lasr-lab/mistac/design/distalEnd/cartridgeInnerMesh.step

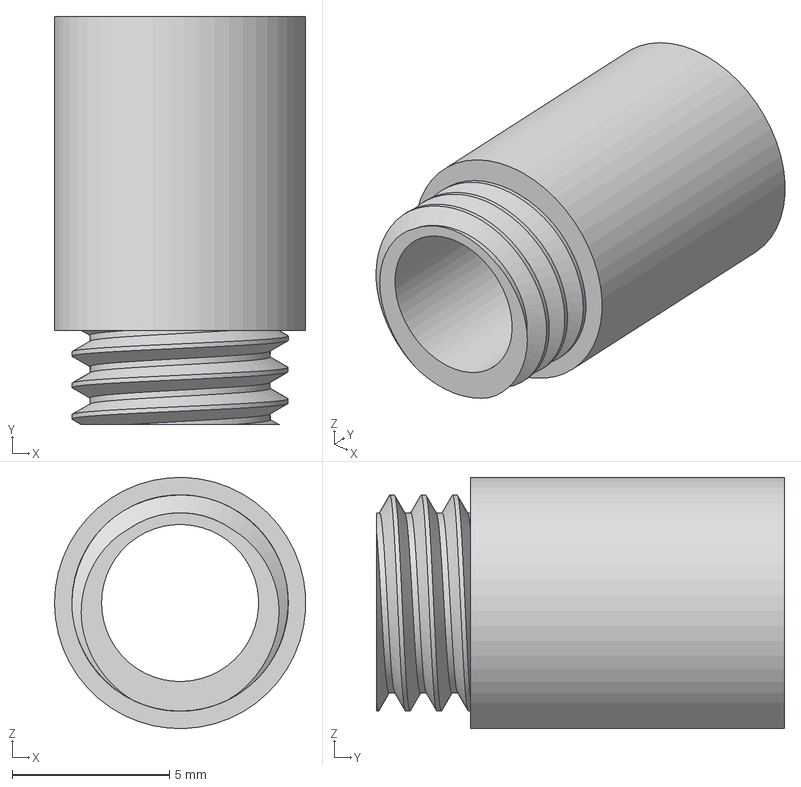
[picture p16: CAD file, 2026-08-04]
design/distalEnd/cartridgeInnerMesh.step
7.99 x 13.0 x 8.00 mm
