lasr-lab/mistac/design/proximalEnd/collimator/fiberFrictionFastener.step

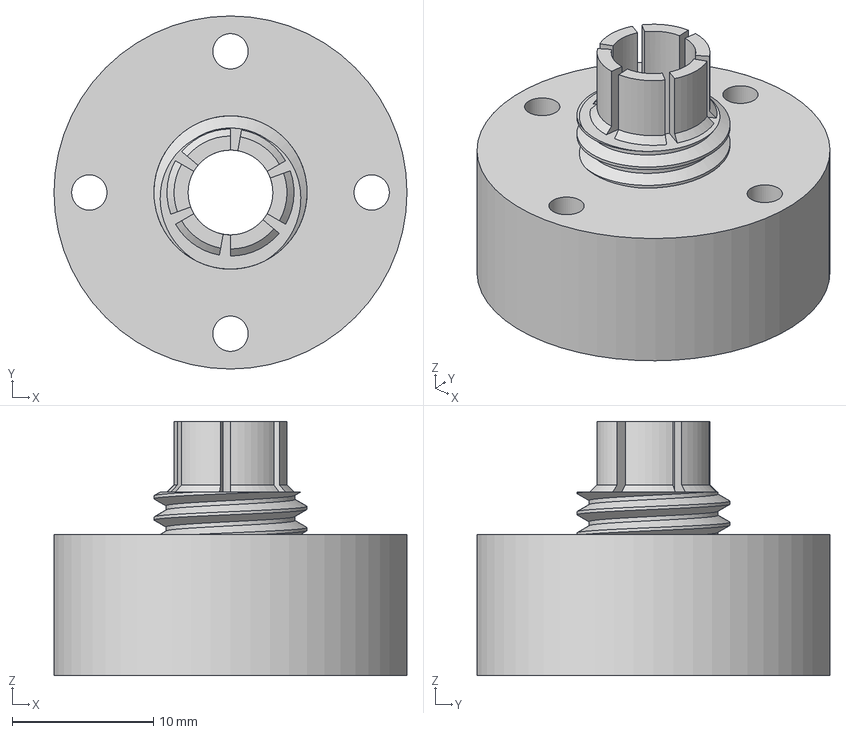
[picture p17: CAD file, 2026-08-04]
design/proximalEnd/collimator/fiberFrictionFastener.step
25.0 x 25.0 x 18.0 mm
