lasr-lab/mistac/design/proximalEnd/fiberHolder/fiberHolderCase1.step

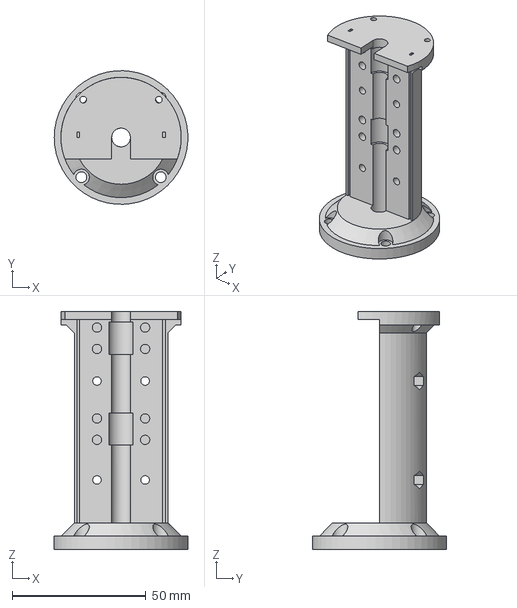
[picture p18: CAD file, 2026-08-04]
design/proximalEnd/fiberHolder/fiberHolderCase1.step
50.0 x 50.0 x 89.0 mm
