lasr-lab/mistac/design/distalEnd/fasteningNutTip.step

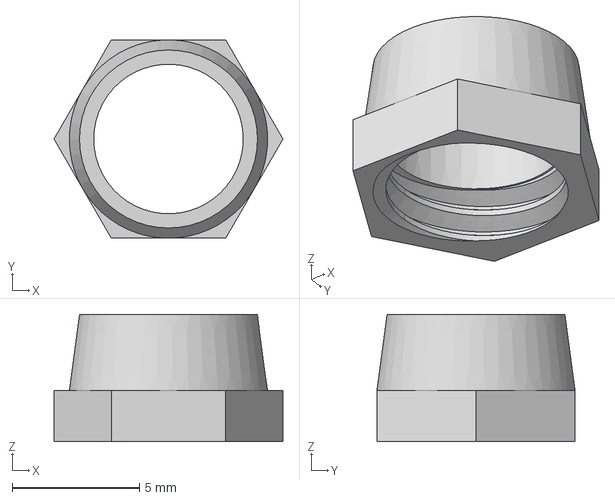
[picture p19: CAD file, 2026-08-04]
design/distalEnd/fasteningNutTip.step
9.01 x 7.80 x 5.00 mm
