lasr-lab/mistac/design/proximalEnd/fiberHolder/fiberFixationBracketInner.step

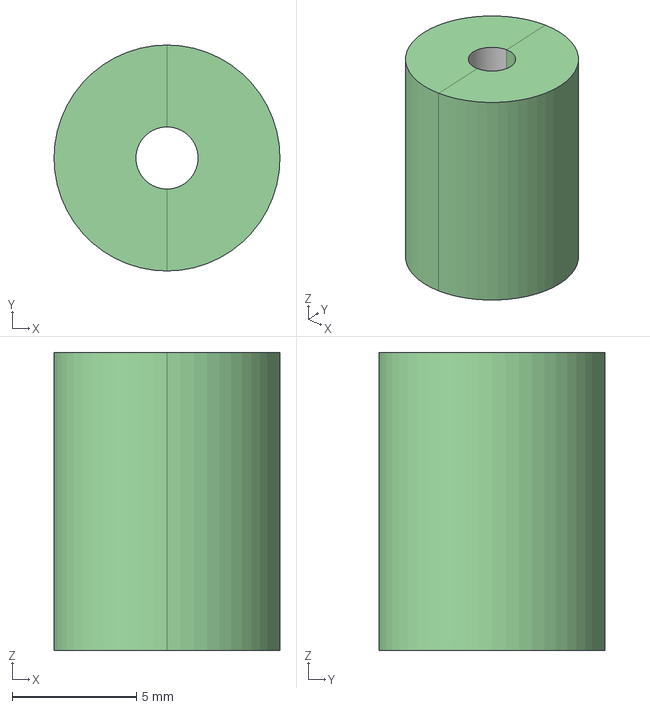
[picture p20: CAD file, 2026-08-04]
design/proximalEnd/fiberHolder/fiberFixationBracketInner.step
9.10 x 9.10 x 12.0 mm
