lasr-lab/mistac/design/distalEnd/cartridgeUndercut.step

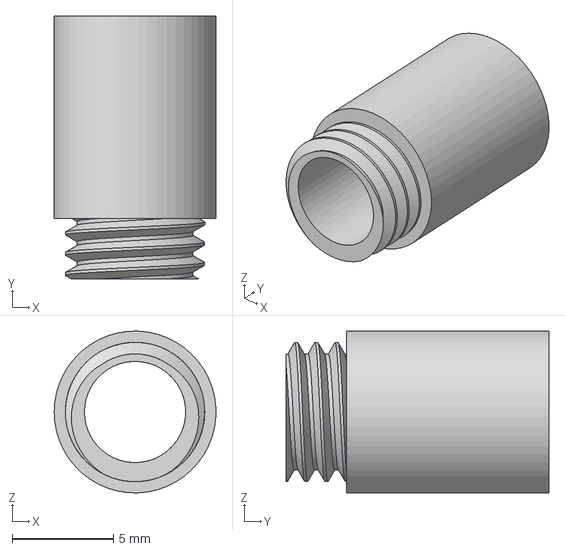
[picture p21: CAD file, 2026-08-04]
design/distalEnd/cartridgeUndercut.step
7.99 x 13.0 x 8.00 mm
