lasr-lab/mistac/design/proximalEnd/fiberHolder/espHolder.step

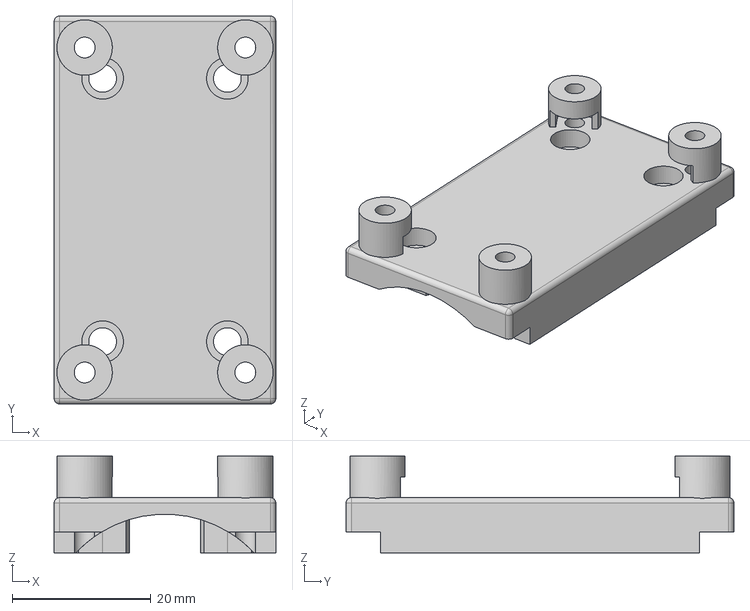
[picture p22: CAD file, 2026-08-04]
design/proximalEnd/fiberHolder/espHolder.step
32.0 x 56.0 x 14.0 mm
