lasr-lab/mistac/design/distalEnd/moldCartrdigeHolder.step

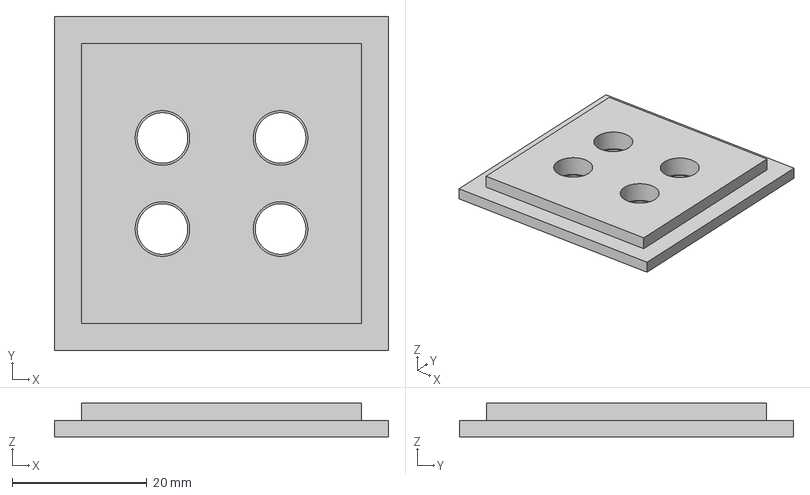
[picture p23: CAD file, 2026-08-04]
design/distalEnd/moldCartrdigeHolder.step
49.5 x 49.5 x 5.00 mm
