lasr-lab/mistac/design/proximalEnd/fiberHolder/adjustmentMechanismConnectorFiberHolder.step

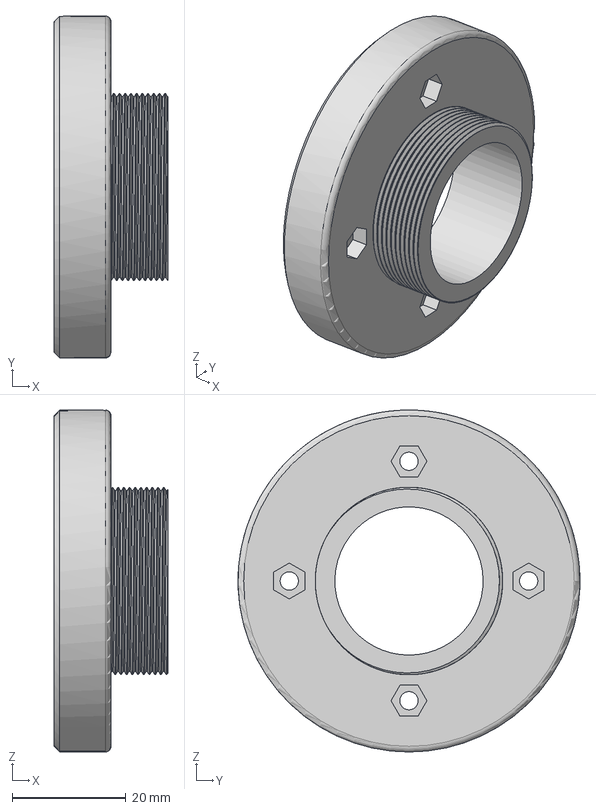
[picture p24: CAD file, 2026-08-04]
design/proximalEnd/fiberHolder/adjustmentMechanismConnectorFiberHolder.step
20.0 x 60.0 x 60.0 mm
