lasr-lab/mistac/design/distalEnd/moldHolder.step

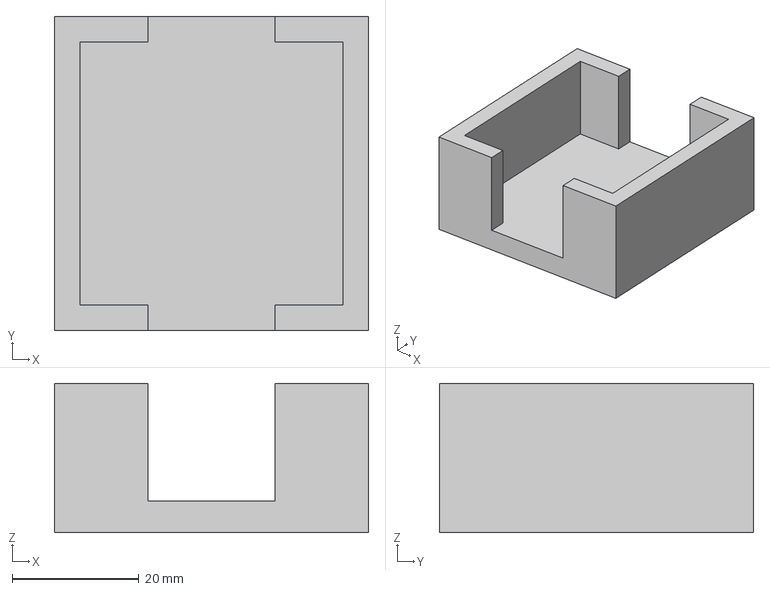
[picture p25: CAD file, 2026-08-04]
design/distalEnd/moldHolder.step
49.5 x 49.5 x 23.5 mm
