lasr-lab/mistac/design/proximalEnd/fiberHolder/fiberFixationBracketOuter.step

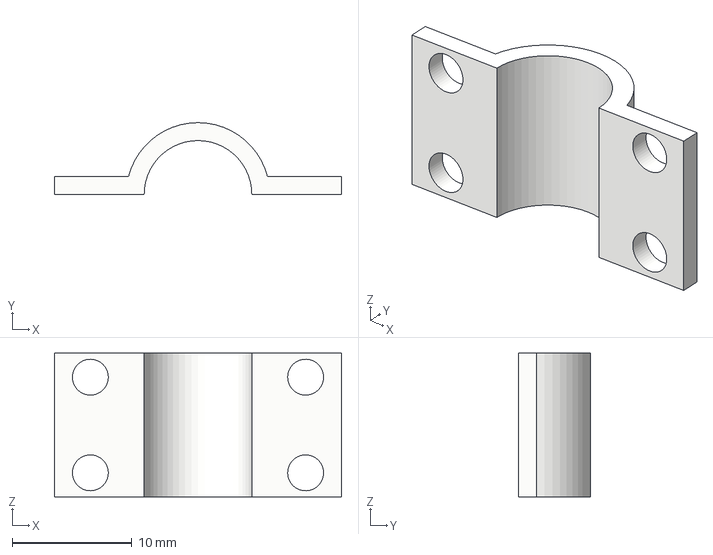
[picture p26: CAD file, 2026-08-04]
design/proximalEnd/fiberHolder/fiberFixationBracketOuter.step
24.0 x 6.00 x 12.0 mm
