lasr-lab/mistac/design/proximalEnd/fiberHolder/adjustmentMechanismConnectorObjective.step

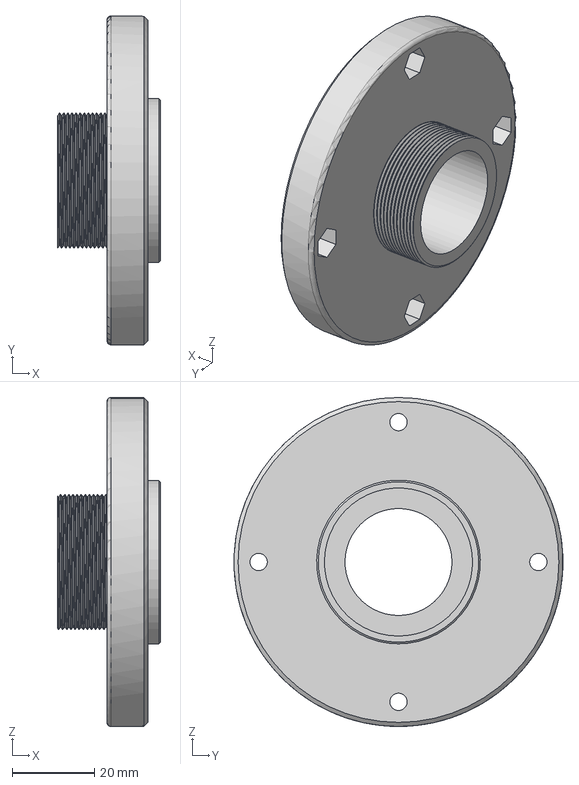
[picture p27: CAD file, 2026-08-04]
design/proximalEnd/fiberHolder/adjustmentMechanismConnectorObjective.step
25.0 x 80.0 x 80.0 mm
